TeamClockworks-RO108/Boron/STL/ShellyBase.stl

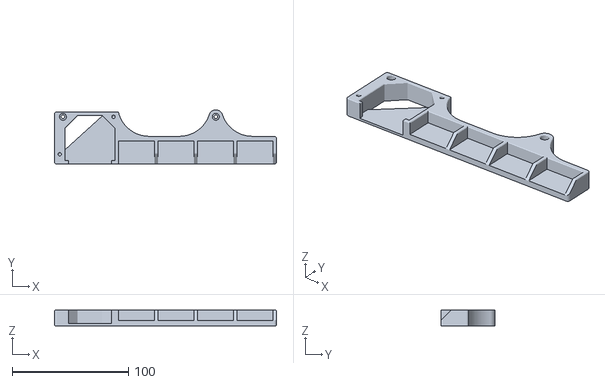
[picture p20: CAD file, 2025-11-24]
STL/ShellyBase.stl
191.0 x 46.8 x 13.7
