TeamClockworks-RO108/Boron/STL/Corner.stl

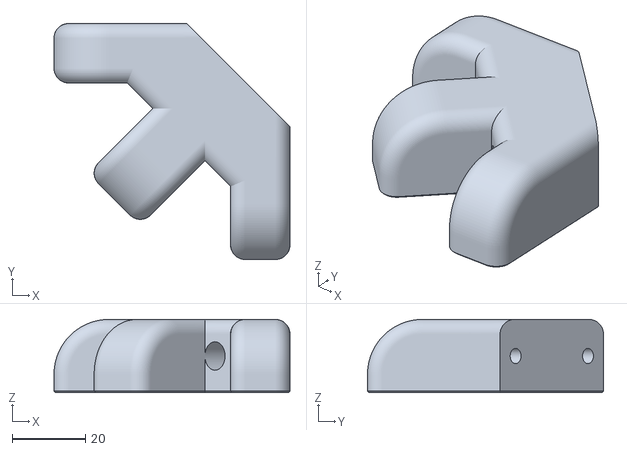
[picture p21: CAD file, 2025-11-24]
STL/Corner.stl
64.5 x 64.5 x 20.0
