TeamClockworks-RO108/Boron/STL/UtilityPanel.stl

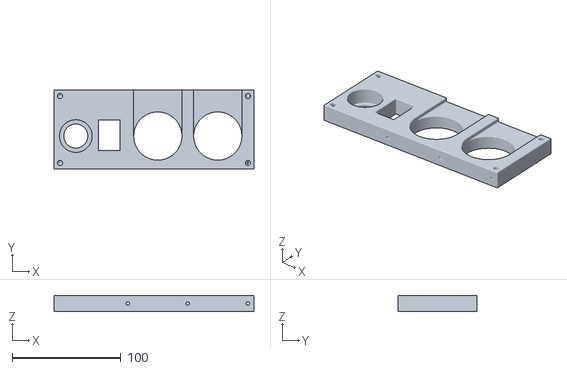
[picture p22: CAD file, 2025-11-24]
STL/UtilityPanel.stl
183.5 x 72.5 x 15.0
