TeamClockworks-RO108/Boron/STL/TopBar.stl

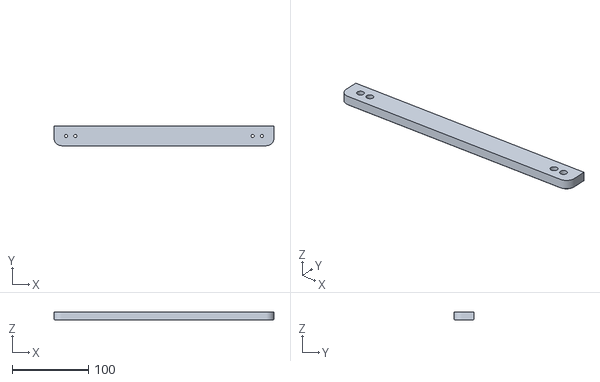
[picture p23: CAD file, 2025-11-24]
STL/TopBar.stl
289.5 x 25.7 x 10.0
