TeamClockworks-RO108/Boron/STL/UHP-350-Mount.stl

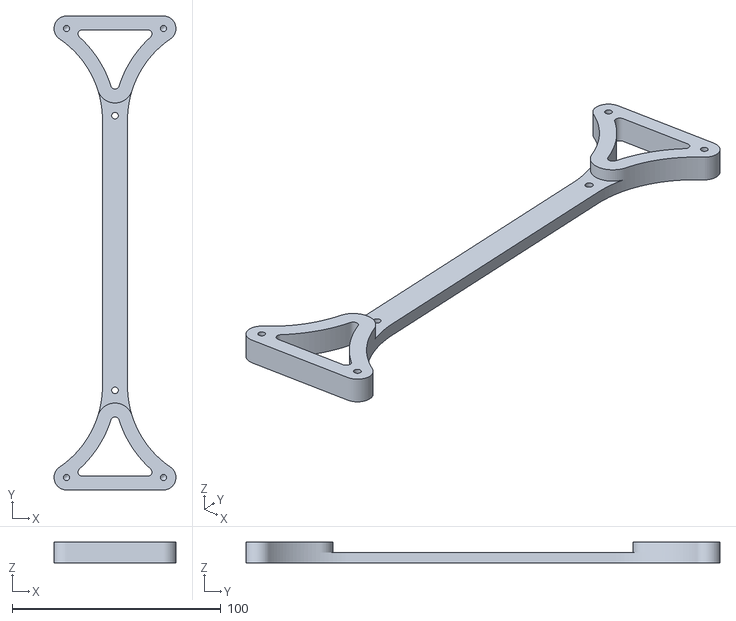
[picture p24: CAD file, 2025-11-24]
STL/UHP-350-Mount.stl
58.4 x 227.0 x 10.0
