TeamClockworks-RO108/Boron/STL/TopCrossbar.stl

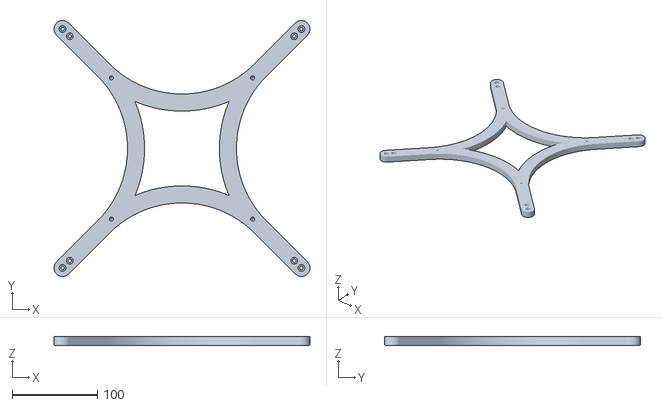
[picture p25: CAD file, 2025-11-24]
STL/TopCrossbar.stl
299.8 x 299.8 x 10.0
